mastensg/windportal/doc/photos/IMG_20181002_153915.jpg

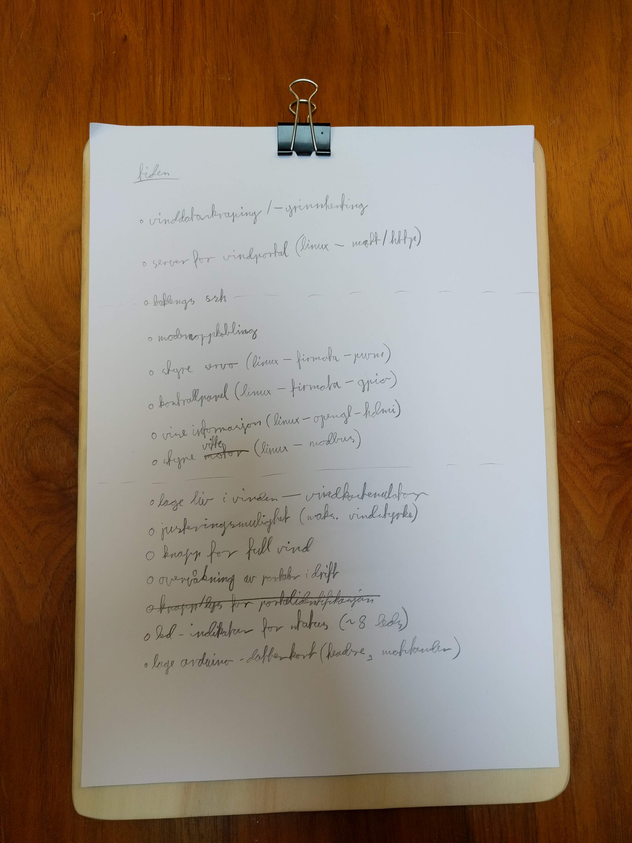
doc/photos/IMG_20181002_153915.jpg
