mastensg/windportal/doc/photos/IMG_20181002_153926.jpg

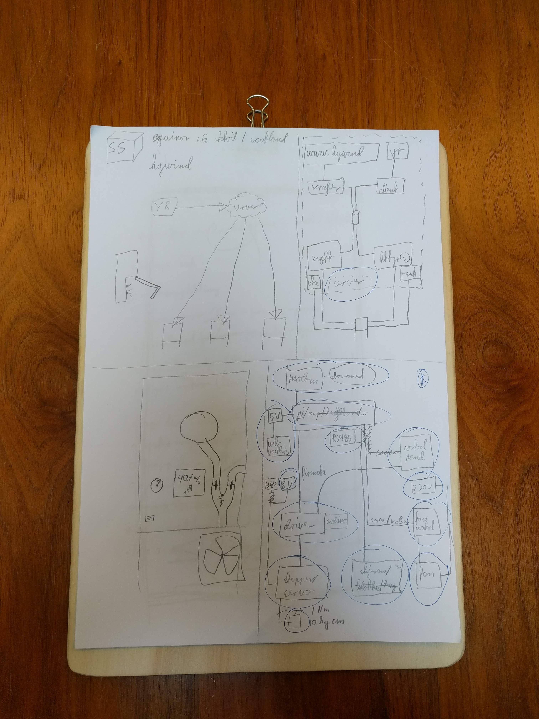
doc/photos/IMG_20181002_153926.jpg
