mastensg/windportal/firmware/wp_ipc.py

#!/usr/bin/env python3

import sys
import json

import zmq
import gevent

PUB_URL = "ipc:///tmp/wp_pub"
SUB_URL = "ipc:///tmp/wp_sub"


class Session:
    def __init__(self):
        self.context = zmq.Context()

        self.sub = self.context.socket(zmq.SUB)
        self.sub.connect(SUB_URL)
        self.sub.setsockopt(zmq.SUBSCRIBE, b"")

        self.poller = zmq.Poller()
        self.poller.register(self.sub, zmq.POLLIN)

        self.pub = self.context.socket(zmq.PUB)
        self.pub.connect(PUB_URL)

    def recv(self, timeout_ms=10):
        values = {}

        while True:
            socks = dict(self.poller.poll(timeout_ms))
            if 0 == len(socks):
                break

            if self.sub in socks:
                message = self.sub.recv_string()
                topic, value = message.split()
                values[topic] = json.loads(value)

        return values

    def send(self, topic, value):
        self.pub.send_string("{} {}".format(topic, json.dumps(value)))


def main():
    """ Print all published messages.
    """
    s = Session()

    args = sys.argv[1:]

    send_message = False
    if len(args) == 2:
        send_message = True
        key, value = args

    if send_message:
        gevent.sleep(0.5) # make sure Session is up
        print('sending {}={}'.format(key, value))
        s.send(key, json.loads(value))
        r = s.recv(timeout_ms=500)
        gevent.sleep(0.5)

    else:
        print('listening for messages')
        while True:
            r = s.recv()
            if {} != r:
                print(r, flush=True)


if __name__ == "__main__":
    main()
